ujwalsahu123/Tara-Scope/1_cliberation/1_acc/using_motor/image.png

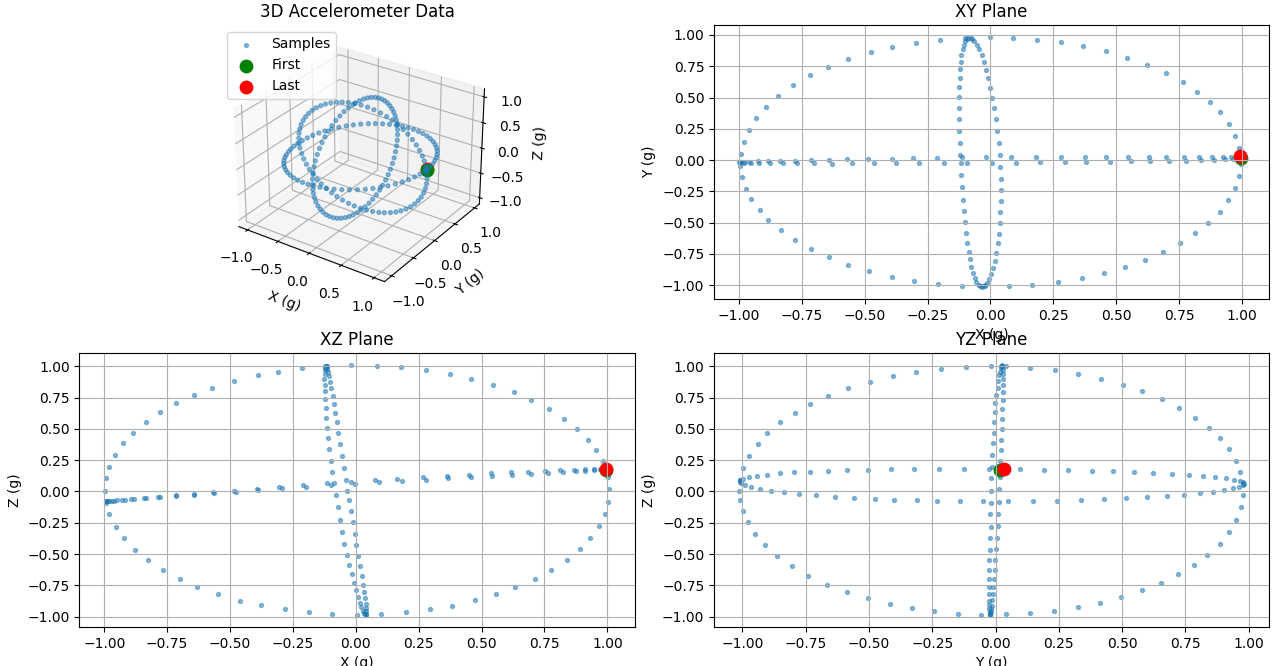
1_cliberation/1_acc/using_motor/image.png
