ujwalsahu123/Tara-Scope/2_sensor-fusion/SF & ARHS study/Screenshot 2025-12-25 184915.png

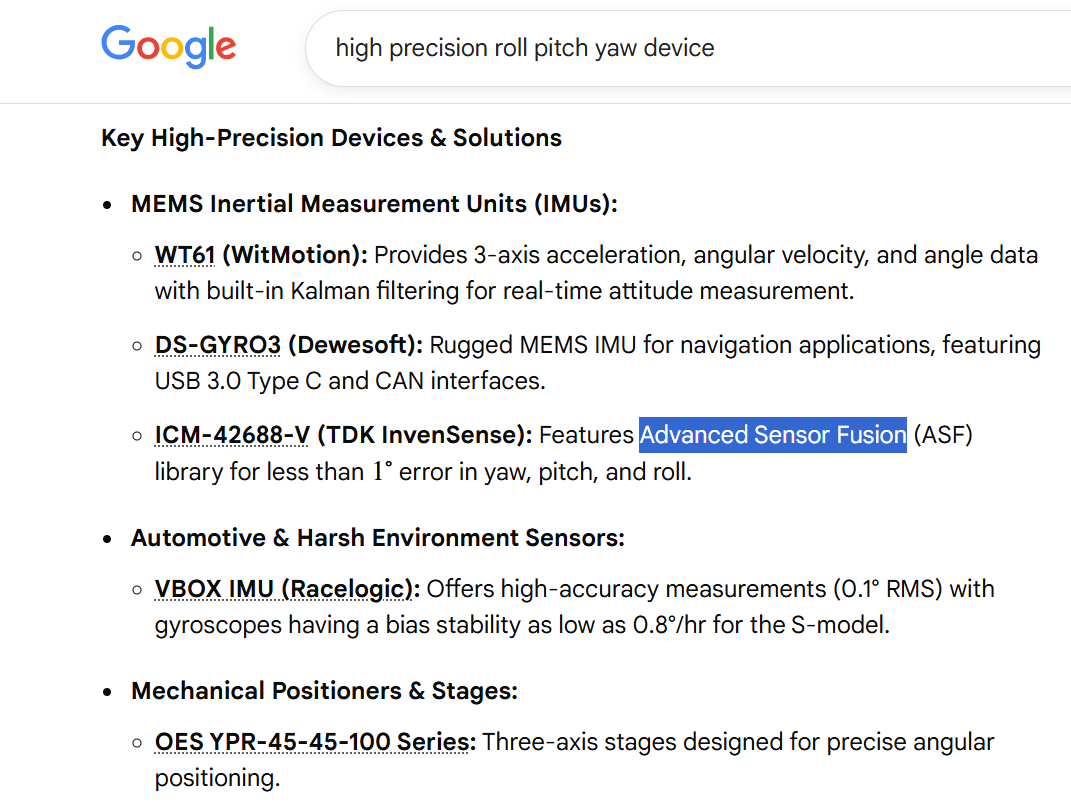
2_sensor-fusion/SF & ARHS study/Screenshot 2025-12-25 184915.png
