ujwalsahu123/Tara-Scope/3_motor-code/IMG-20250927-WA0002.jpg

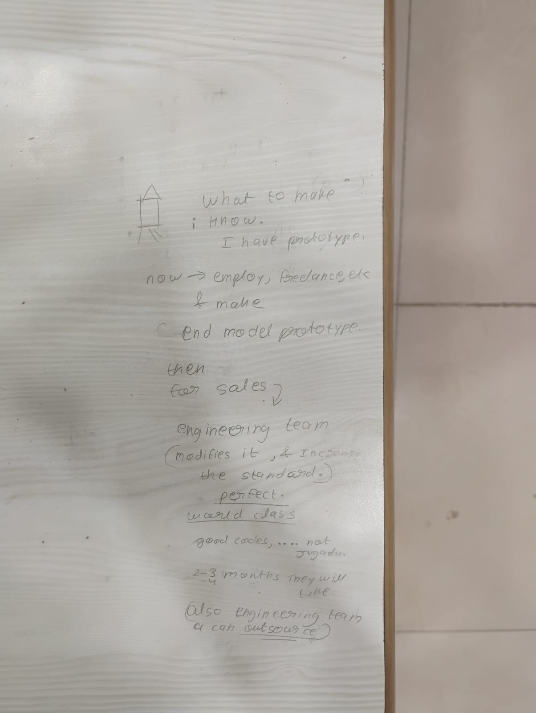
3_motor-code/IMG-20250927-WA0002.jpg
