ujwalsahu123/Tara-Scope/3_motor-code/IMG-20250927-WA0003.jpg

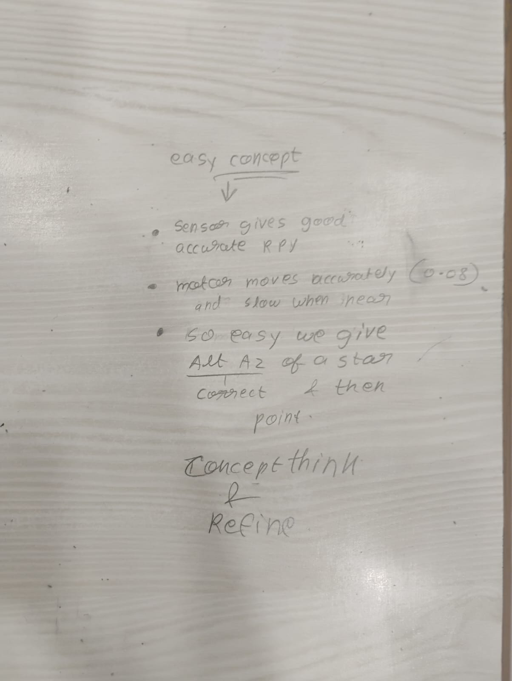
3_motor-code/IMG-20250927-WA0003.jpg
