ujwalsahu123/Tara-Scope/4_star_pointing/flow.jpg

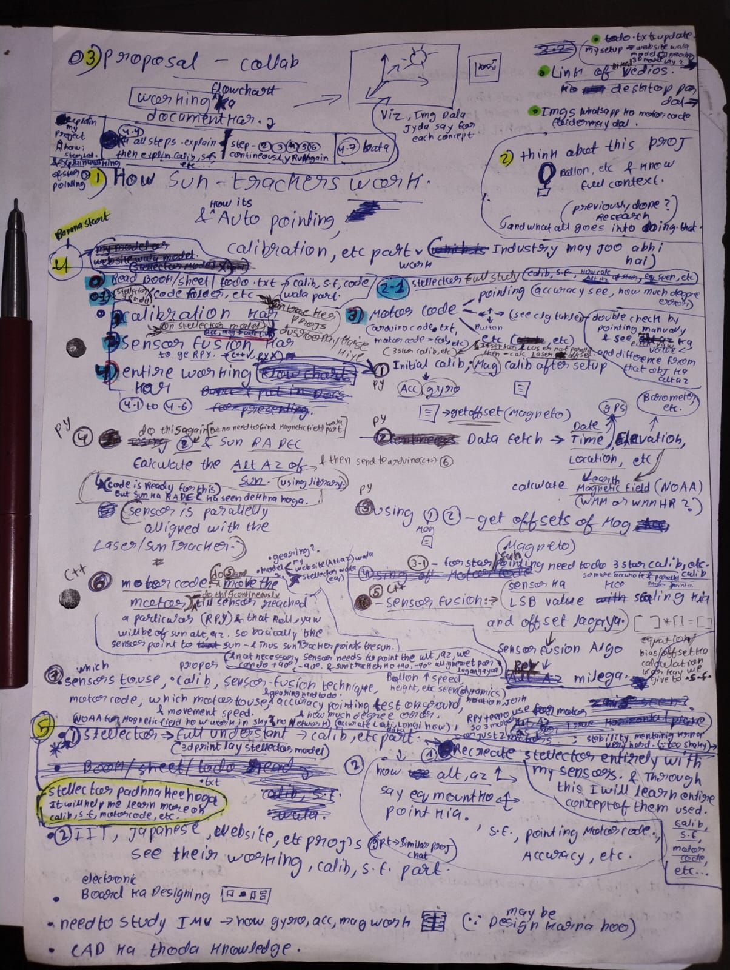
4_star_pointing/flow.jpg
