ujwalsahu123/Tara-Scope/5_desktop app (badiya wala, with list of stars and all)/1_UX_.jpg

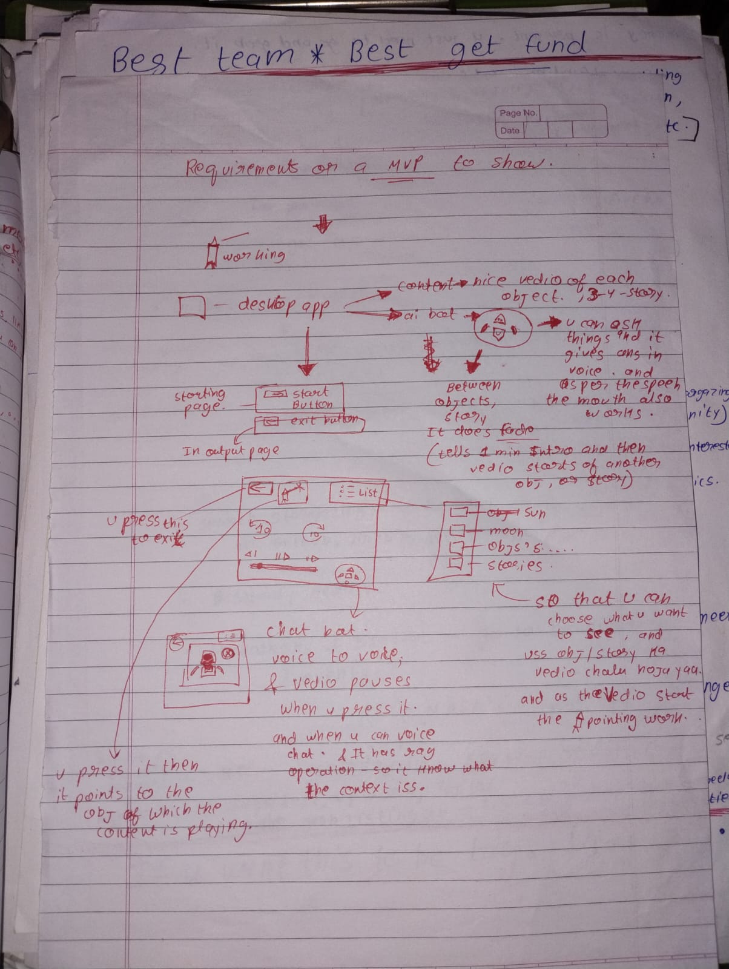
5_desktop app (badiya wala, with list of stars and all)/1_UX_.jpg
