ujwalsahu123/Tara-Scope/video/Screenshot 2025-12-29 133930.png

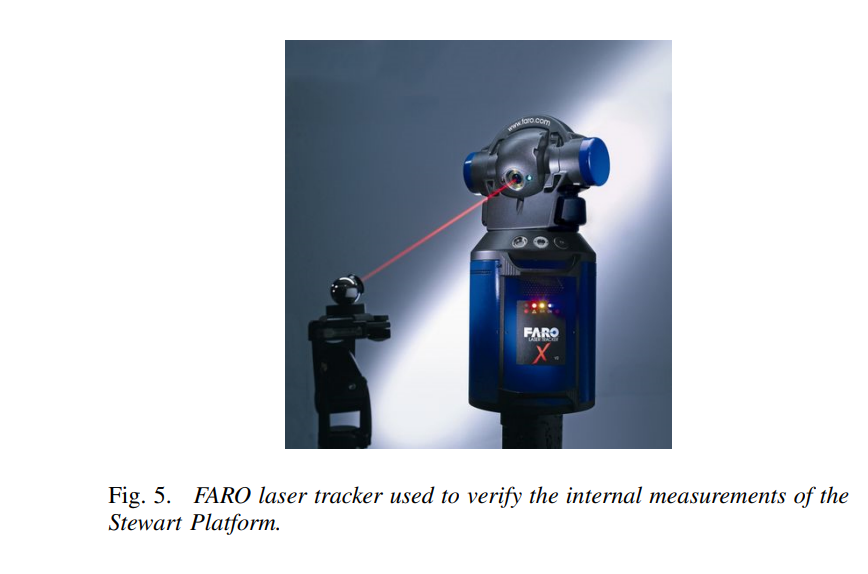
video/Screenshot 2025-12-29 133930.png
