ujwalsahu123/Tara-Scope/1_cliberation/1_acc/using_motor/image_using_2motor_calib_pretty_is_fine(1024_orient_4step_data).png

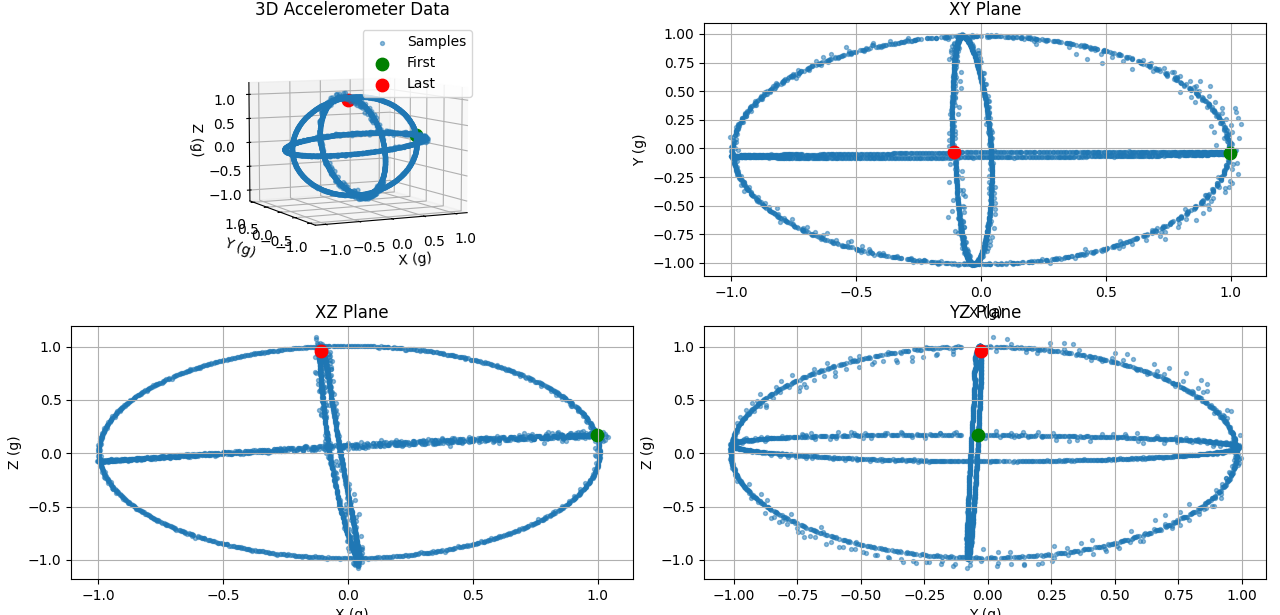
1_cliberation/1_acc/using_motor/image_using_2motor_calib_pretty_is_fine(1024_orient_4step_data).png
