ujwalsahu123/Tara-Scope/3_motor-code/2.2_Pointing-code.ino

// contineously does =>  Raw -> calib -> SF -> RPY
// we give ALT AZ value from Serial Monitor and it moves the motors to point the RPY to ALT AZ. 

// contineously point // or // point and after reached stop .... 
