ujwalsahu123/Tara-Scope/2_sensor-fusion/acc-gyro-sf.ino

// only acc and gryo ka use karke sf kar see whats the problem -> data rate , filtering lag , fifo , ism mmc data rate mismatch, sensor hub , etc... 
// atleast we will get some basic idea. 

// can do RPY or just RP both are fine.
