ujwalsahu123/Tara-Scope/1_cliberation/1_acc/3_calibrate-plot.py

"""

PLOT UNCALIBRTED AND CALIBRATED ACCELEROMETER MEASUREMENTS

Read data file with raw measurements and compare calibrated vs. uncalibrated
measurements.

Code By: Michael Wrona

The calibration equation is:
    h_calib = A * (h_meas - b)

h_calib: Calibrated measurements (3x1)
A: Scale factor and misalignment correction matrix (3x3, symmetric)
h_meas: Raw measurements (3x1)
b: Biases correction vector (3x1)

Calibration parametrers were determined by the Magneto calibration software (see Resources).

Resources
---------
Magneto calibration software developed by Sailboat Instruments blog
    https://sites.google.com/site/sailboatinstruments1/home

"""


import numpy as np
import matplotlib.pyplot as plt


# Define calibration parameters
A = np.array([[0.996986, 0.000024, -0.000549], 
              [0.000024, 1.001778, 0.000595],
              [-0.000549, 0.000595, 1.003680]])

b = np.array([0.005380, -0.014230, 0.009798])

# Read data and apply calibration and plot 
################## file name ##############################
rawData = np.genfromtxt('using_motor/data_g_2g_0filter.txt', delimiter='\t')  # raw measurement file
units = 'G\'s'  # units of accelerometer measurements (used for axis labels)

N = len(rawData)
calibData = np.zeros((N, 3), dtype='float')
for i in range(N):
    currMeas = np.array([rawData[i, 0], rawData[i, 1], rawData[i, 2]])
    calibData[i, :] = A @ (currMeas - b)

# Plot XY data
plt.figure()
plt.plot(rawData[:, 0], rawData[:, 1], 'b*', label='Raw Meas.')
plt.plot(calibData[:, 0], calibData[:, 1], 'r*', label='Calibrated Meas.')
plt.title('XY Accelerometer Data')
plt.xlabel('X [{}]'.format(units))
plt.ylabel('Y [{}]'.format(units))
plt.legend()
plt.grid()
plt.axis('equal')

# Plot YZ data
plt.figure()
plt.plot(rawData[:, 1], rawData[:, 2], 'b*', label='Raw Meas.')
plt.plot(calibData[:, 1], calibData[:, 2], 'r*', label='Calibrated Meas.')
plt.title('YZ Accelerometer Data')
plt.xlabel('Y [{}]'.format(units))
plt.ylabel('Z [{}]'.format(units))
plt.legend()
plt.grid()
plt.axis('equal')

# Plot XZ data
plt.figure()
plt.plot(rawData[:, 0], rawData[:, 2], 'b*', label='Raw Meas.')
plt.plot(calibData[:, 0], calibData[:, 2], 'r*', label='Calibrated Meas.')
plt.title('XZ Accelerometer Data')
plt.xlabel('X [{}]'.format(units))
plt.ylabel('Z [{}]'.format(units))
plt.legend()
plt.grid()
plt.axis('equal')


# Plot 3D scatter
fig = plt.figure()
ax = fig.add_subplot(111, projection='3d')
for i in range(N):
    xraw = rawData[i, 0]
    yraw = rawData[i, 1]
    zraw = rawData[i, 2]

    xcalib = calibData[i, 0]
    ycalib = calibData[i, 1]
    zcalib = calibData[i, 2]
    ax.scatter(xraw, yraw, zraw, color='r', label='Raw')
    ax.scatter(xcalib, ycalib, zcalib, color='b', label='Calibrated')

ax.set_title('3D Scatter Plot of Accelerometer Data')
ax.set_xlabel('X [{}]'.format(units))
ax.set_ylabel('Y [{}]'.format(units))
ax.set_zlabel('Z [{}]'.format(units))
ax.legend(['Raw', 'Calibrated'])

plt.show()
